libc0607/esp32-vision/img/fpc_cable_with_temt6000_welded_01.jpg

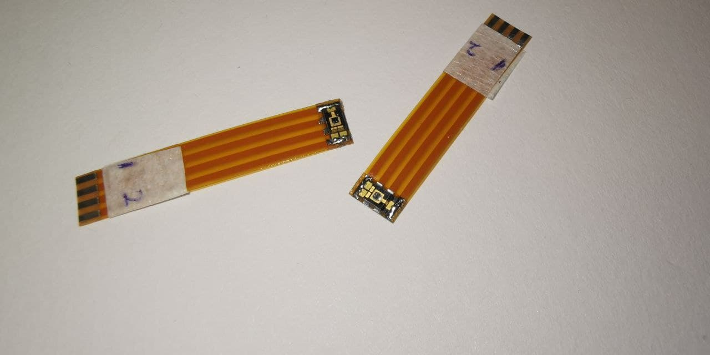
img/fpc_cable_with_temt6000_welded_01.jpg
