libc0607/esp32-vision/img/liyue_v2.1_Qi_coil_with_two_layers_ferrite_sheet_and_module.jpg

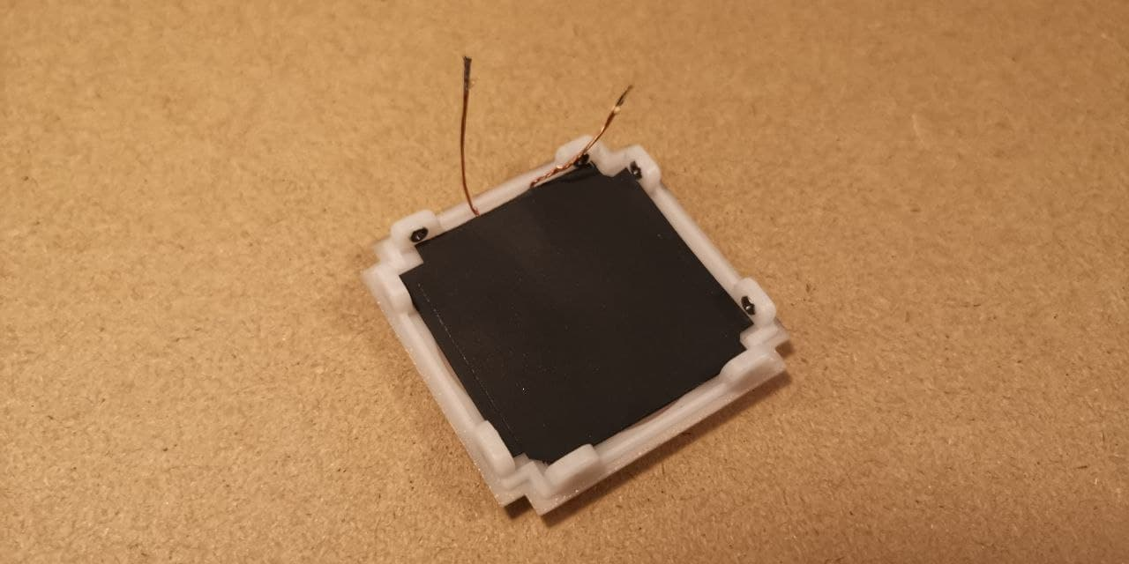
img/liyue_v2.1_Qi_coil_with_two_layers_ferrite_sheet_and_module.jpg
