libc0607/esp32-vision/img/mondstadt_pcb_welding_02.jpg

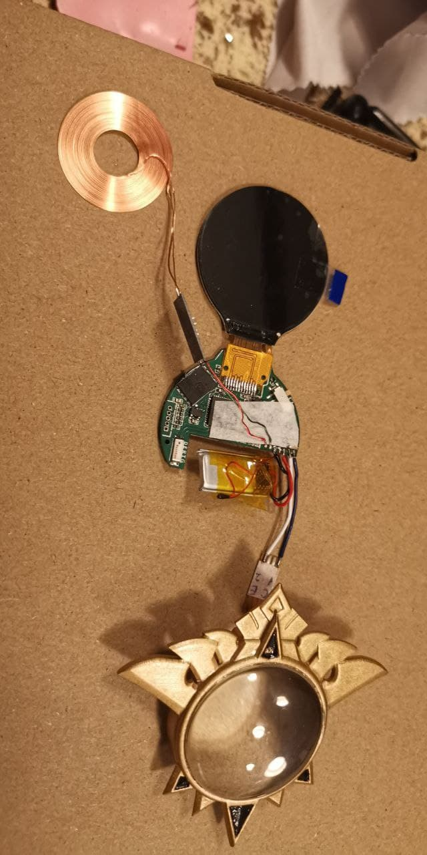
img/mondstadt_pcb_welding_02.jpg
