libc0607/esp32-vision/src/vision_SPIFFS_GIF_video/Data/loop.gif

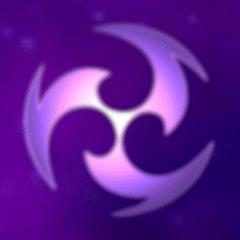
src/vision_SPIFFS_GIF_video/Data/loop.gif
