libc0607/esp32-vision/src/vision_SPIFFS_GIF_video/medikarasenpai-240p-5s-15fps.gif

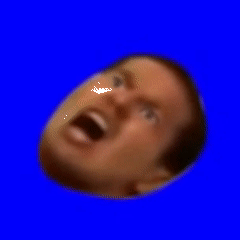
src/vision_SPIFFS_GIF_video/medikarasenpai-240p-5s-15fps.gif
